jadutter/NGC602/Draft 1.JPG

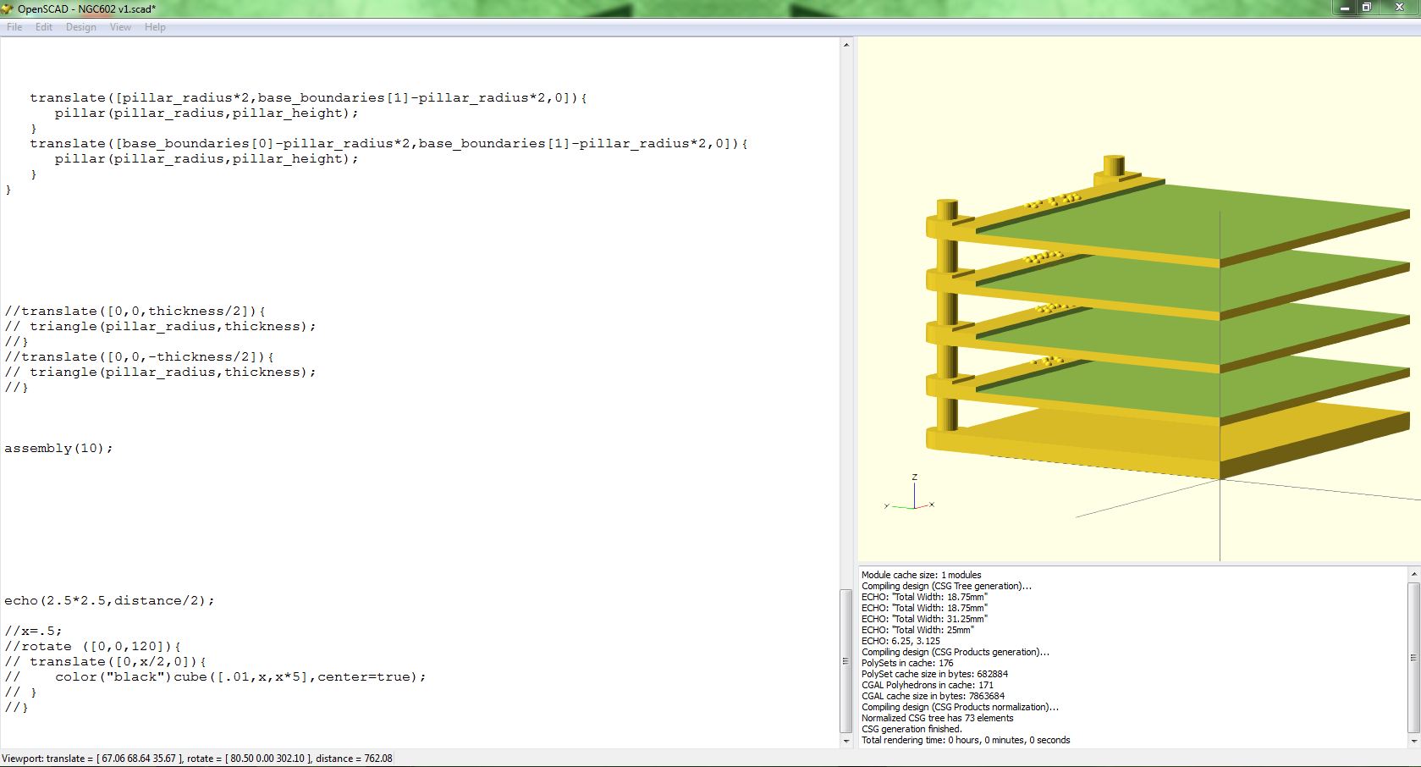
Draft 1.JPG
