jadutter/NGC602/Draft 2.JPG

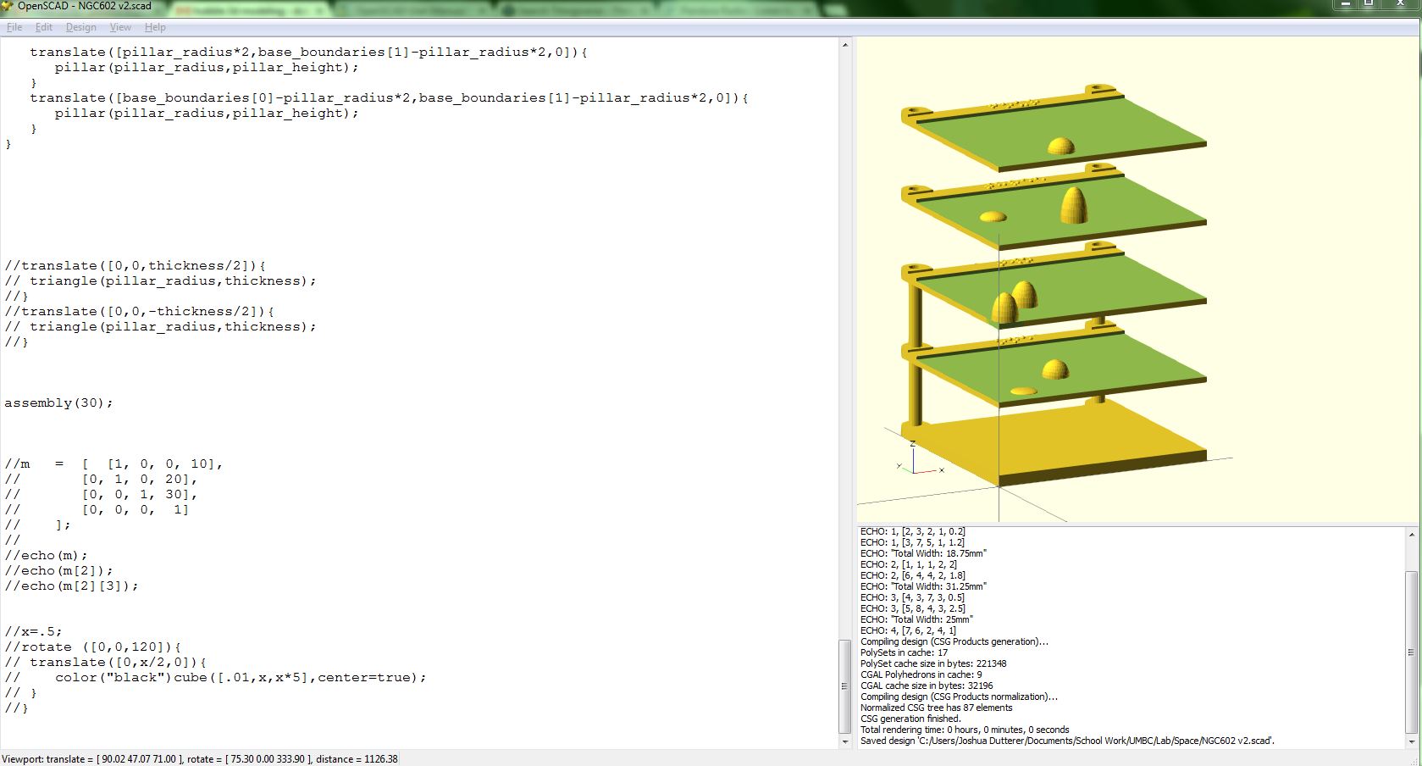
Draft 2.JPG
