jadutter/NGC602/Draft 3 All.JPG

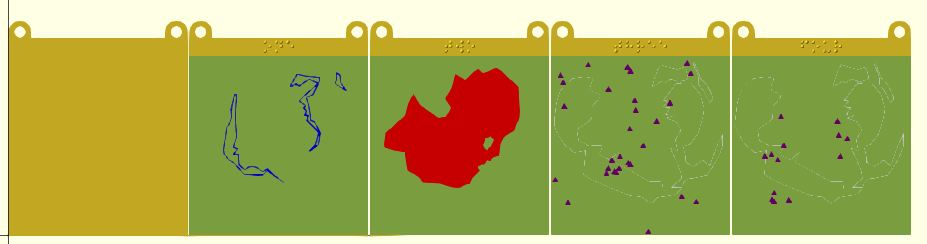
Draft 3 All.JPG
