jadutter/NGC602/Draft 3 plate 1.JPG

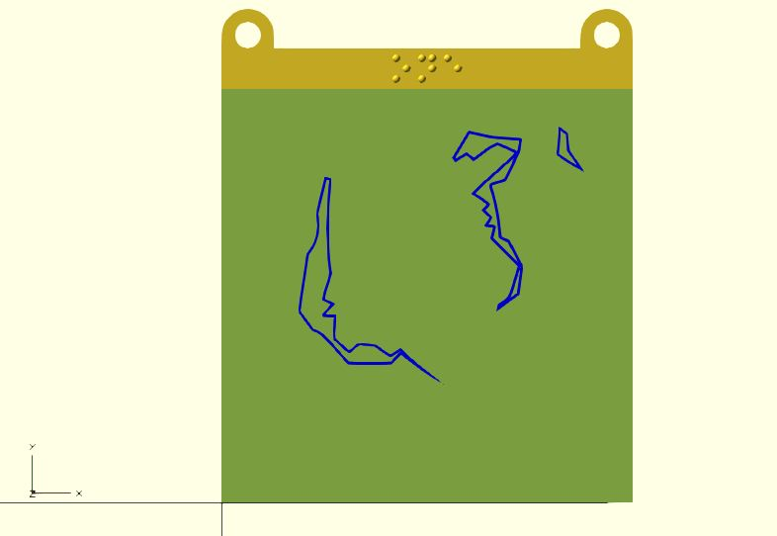
Draft 3 plate 1.JPG
