jadutter/NGC602/Draft 3 plate 2.JPG

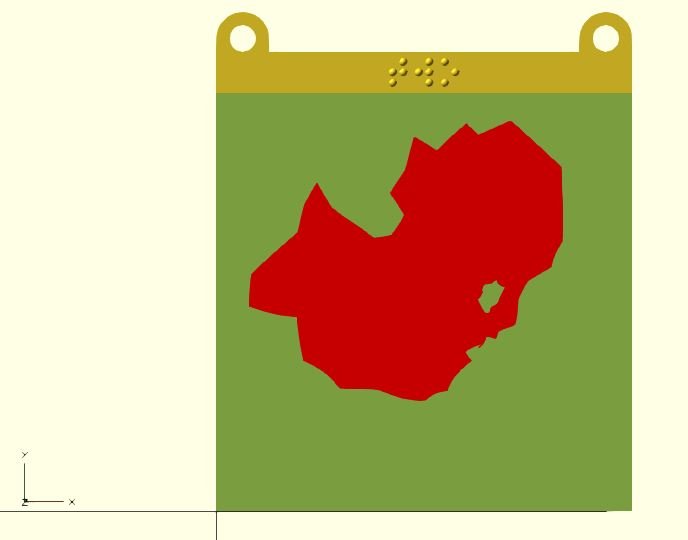
Draft 3 plate 2.JPG
