jadutter/NGC602/Draft 3 plate 3&4 again.JPG

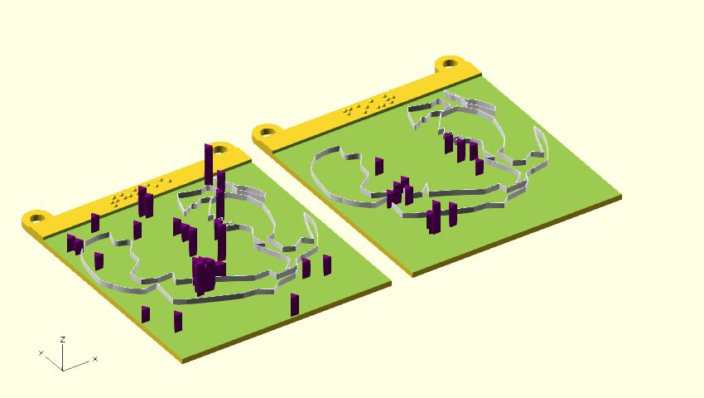
Draft 3 plate 3&4 again.JPG
