jadutter/NGC602/Draft 3 plate 4.JPG

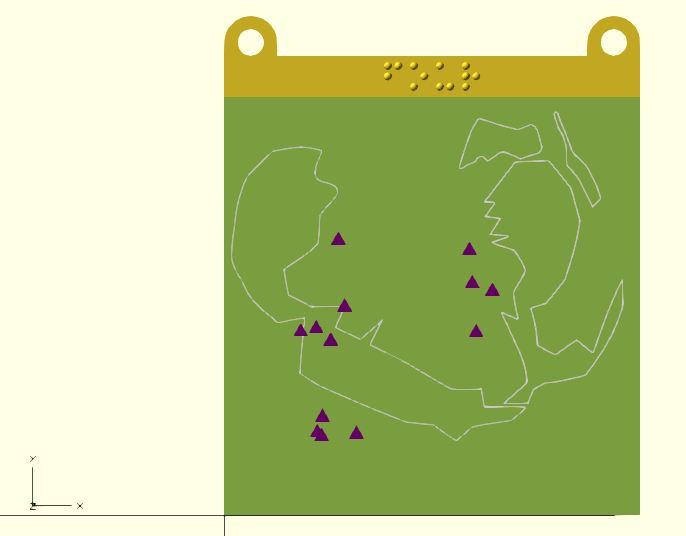
Draft 3 plate 4.JPG
