jadutter/NGC602/Draft 4 plate 3 again.JPG

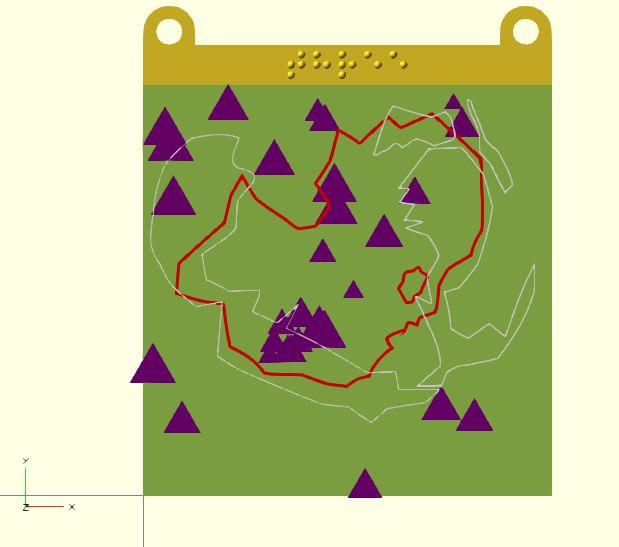
Draft 4 plate 3 again.JPG
