jadutter/NGC602/Draft 4 plate 3.JPG

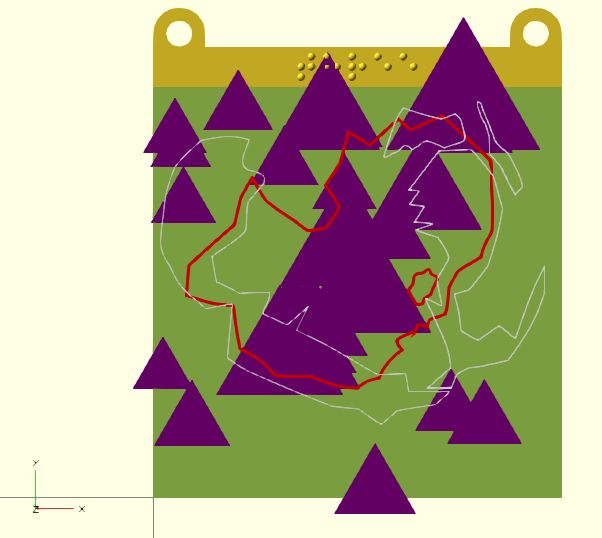
Draft 4 plate 3.JPG
