jadutter/NGC602/Draft 5 plate 3&4.JPG

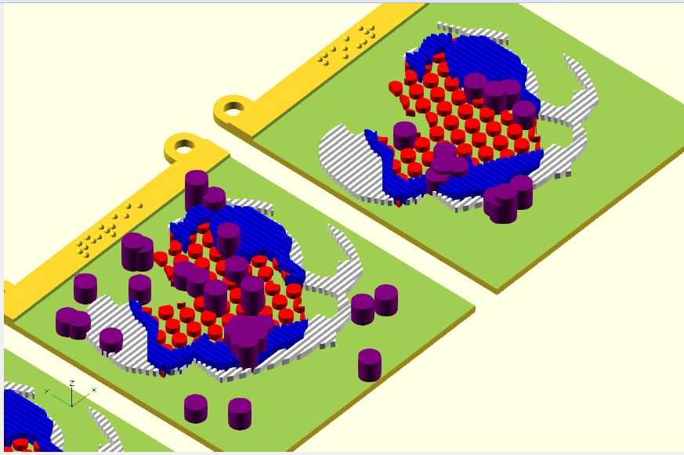
Draft 5 plate 3&4.JPG
