jadutter/NGC602/Extruded Gas.JPG

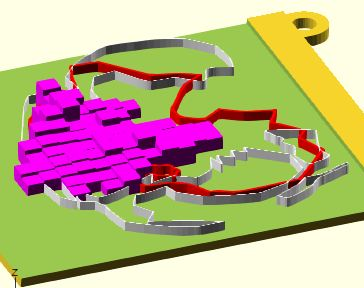
Extruded Gas.JPG
