jadutter/NGC602/Grice-RevisedNGC602Textures.jpg

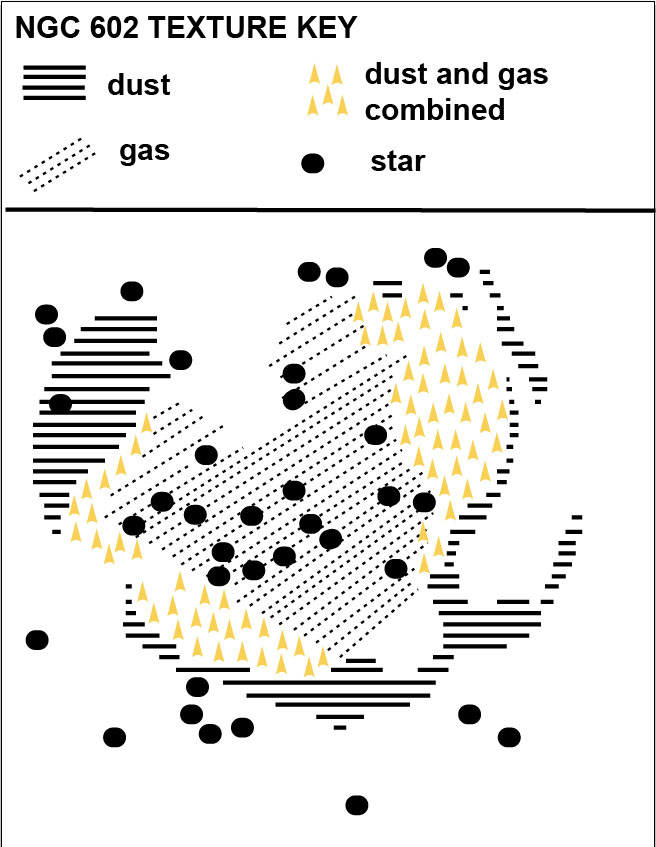
Grice-RevisedNGC602Textures.jpg
