jadutter/NGC602/IMG_20130621_184517_456.jpg

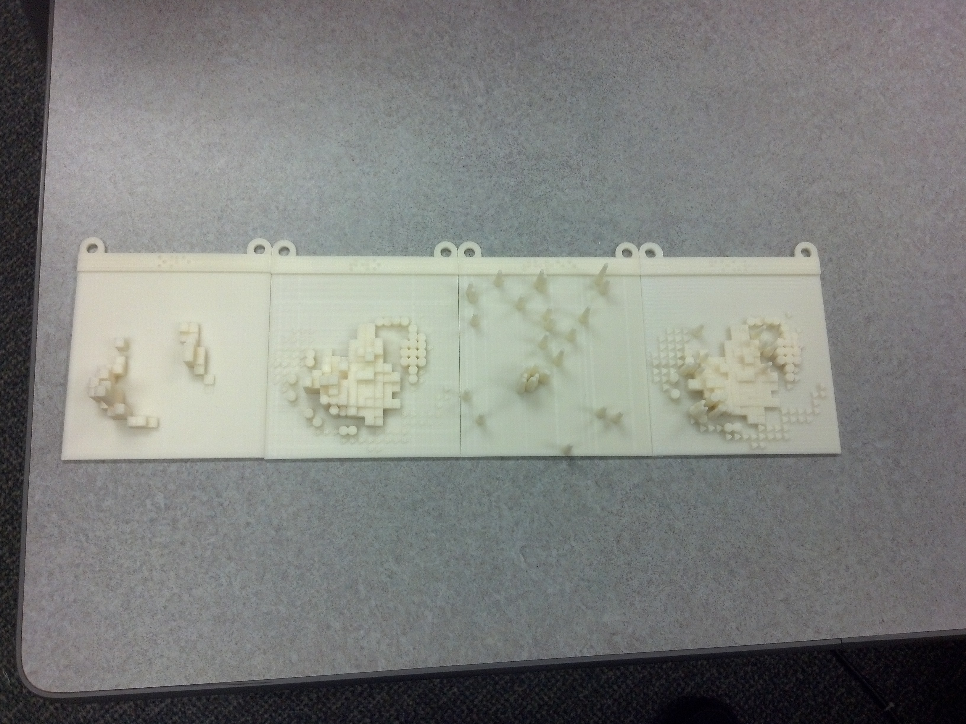
IMG_20130621_184517_456.jpg
