jadutter/NGC602/IMG_20130621_184525_783.jpg

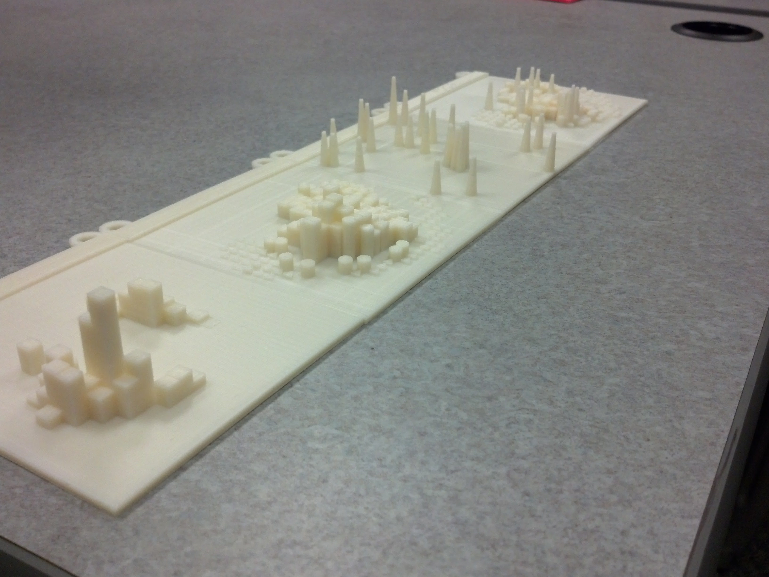
IMG_20130621_184525_783.jpg
