jadutter/NGC602/IMG_20130625_030818_657.jpg

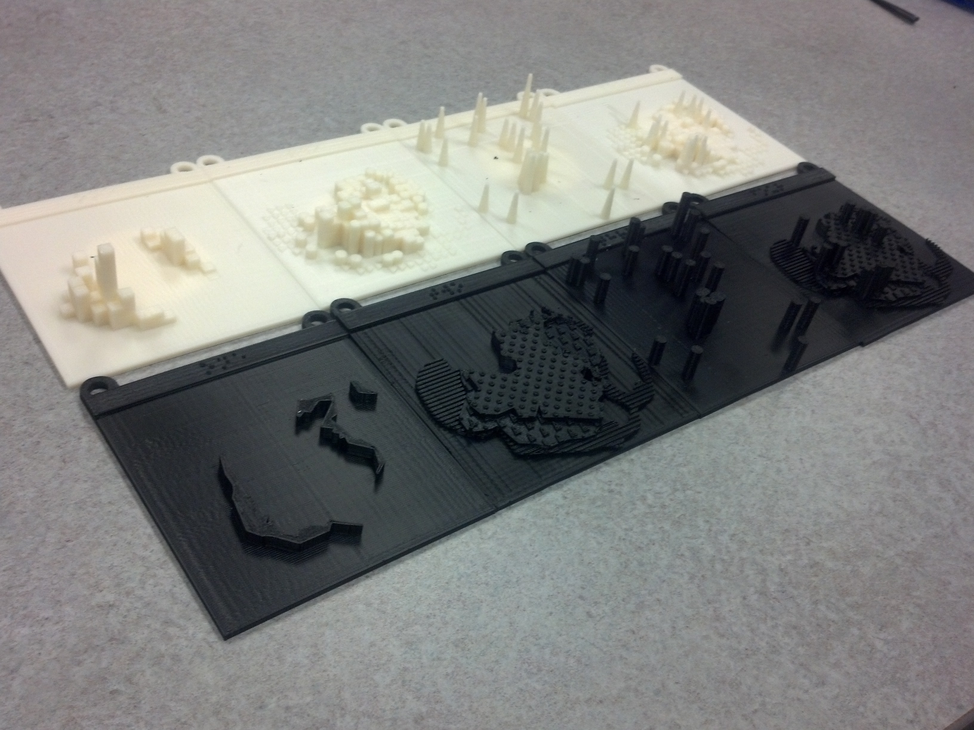
IMG_20130625_030818_657.jpg
