jadutter/NGC602/IMG_20130625_030837_733.jpg

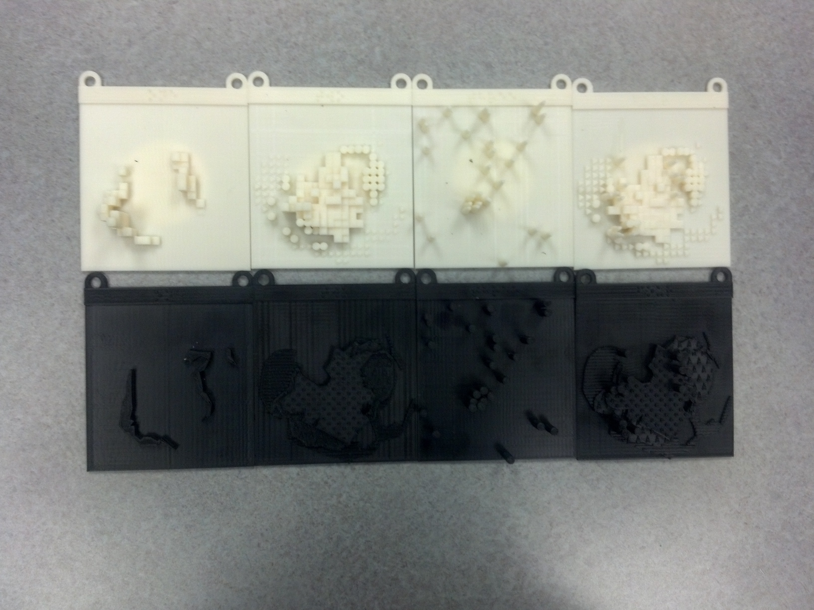
IMG_20130625_030837_733.jpg
