jadutter/NGC602/IMG_20130625_030843_815.jpg

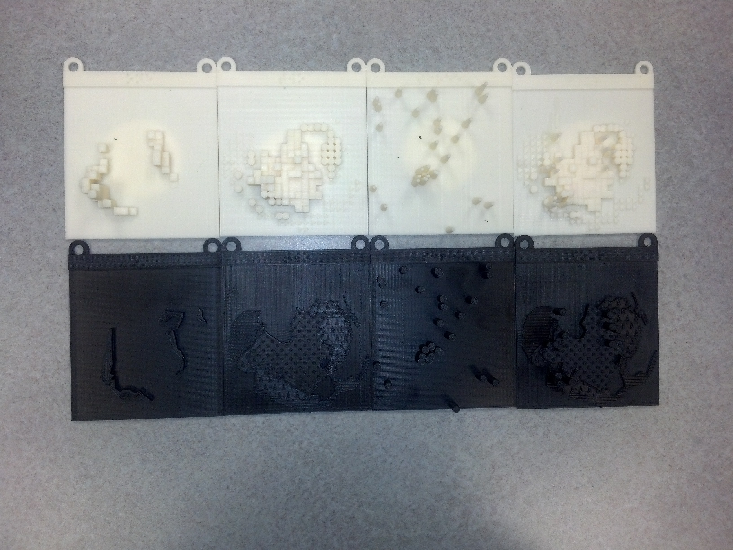
IMG_20130625_030843_815.jpg
