jadutter/NGC602/IMG_20130625_030916_029.jpg

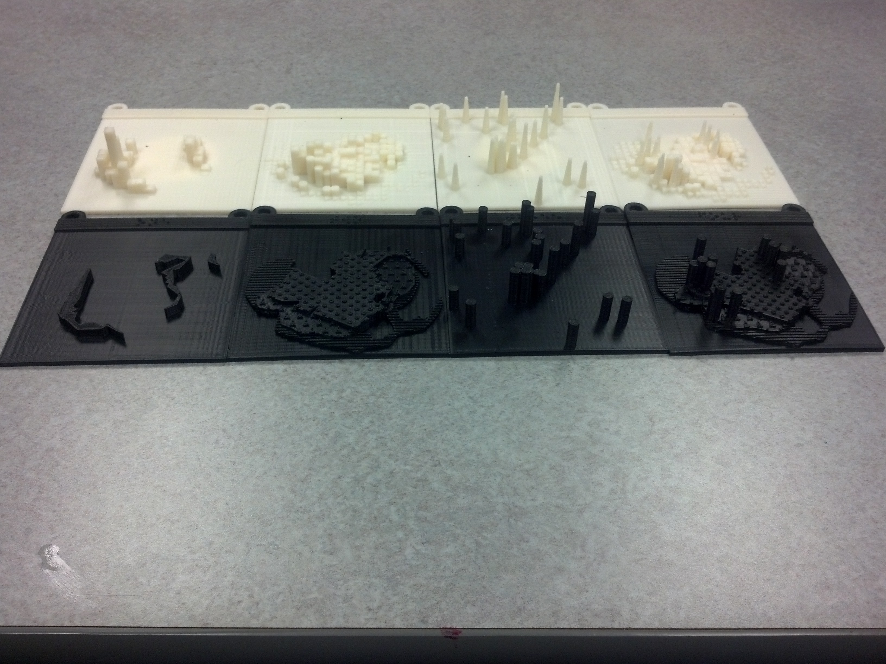
IMG_20130625_030916_029.jpg
