jadutter/NGC602/IMG_20130625_030923_143.jpg

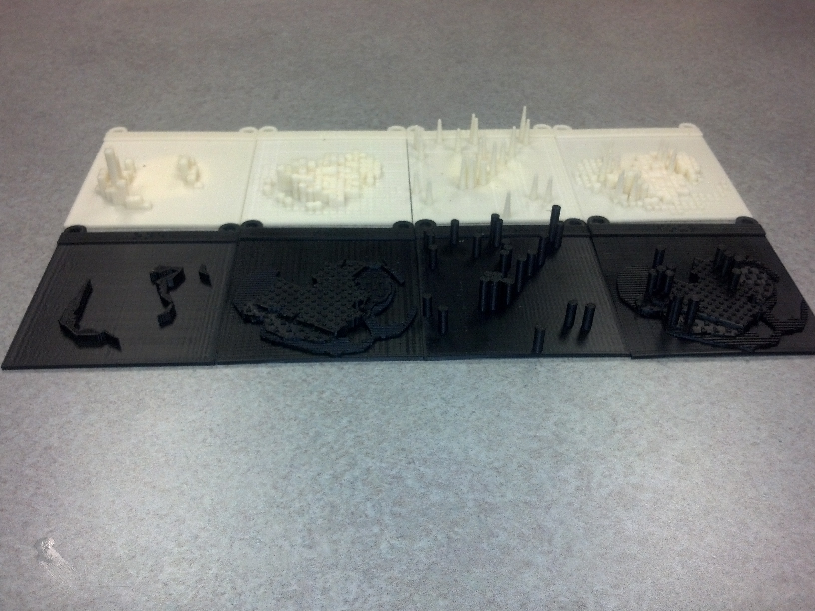
IMG_20130625_030923_143.jpg
