jadutter/NGC602/IMG_20130625_030944_318.jpg

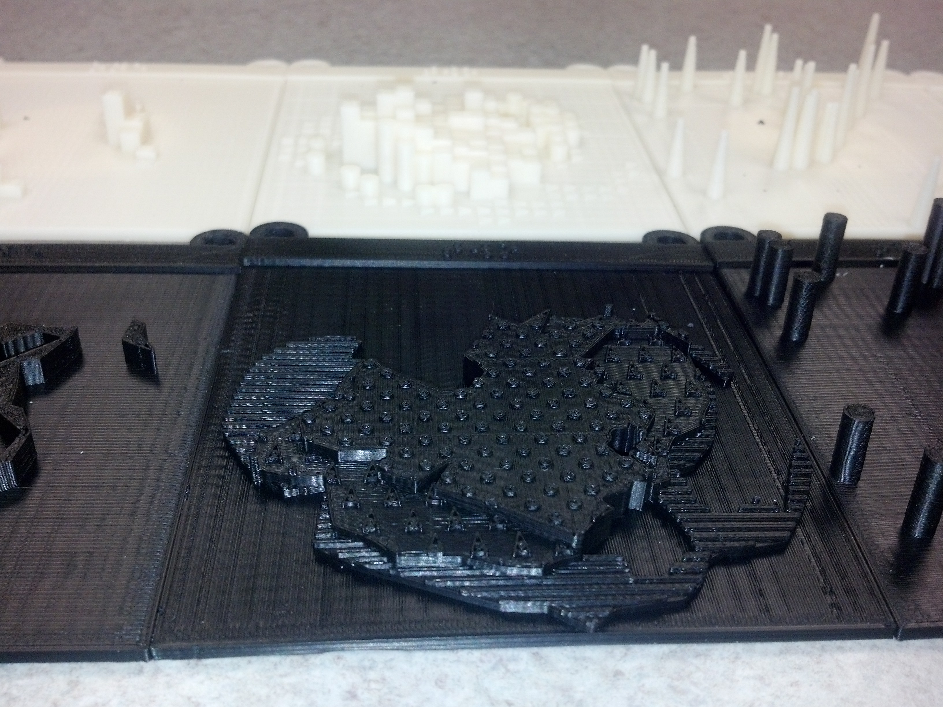
IMG_20130625_030944_318.jpg
