jadutter/NGC602/IMG_20130625_030954_769.jpg

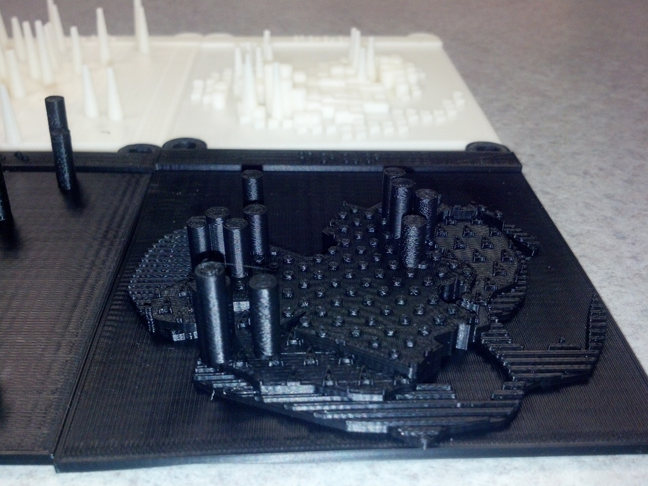
IMG_20130625_030954_769.jpg
