jadutter/NGC602/NGC602 v7 Left Plate 2&3&4.JPG

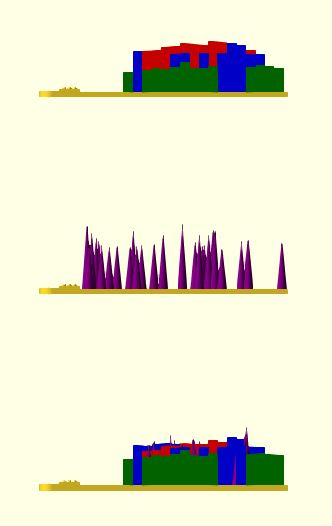
NGC602 v7 Left Plate 2&3&4.JPG
