jadutter/NGC602/NGC602 v7 Left Plate 3, again.JPG

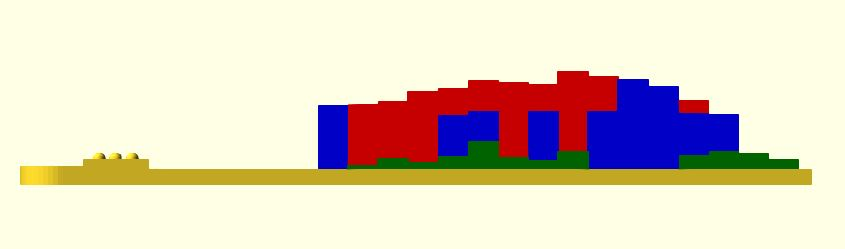
NGC602 v7 Left Plate 3, again.JPG
