jadutter/NGC602/NGC602 v7 Left Plate 4, again.JPG

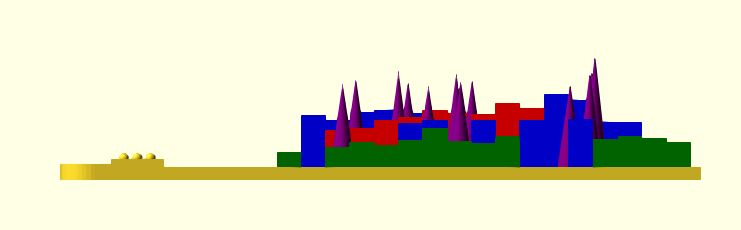
NGC602 v7 Left Plate 4, again.JPG
