jadutter/NGC602/NGC602 v7 Plate 3 Scaled.JPG

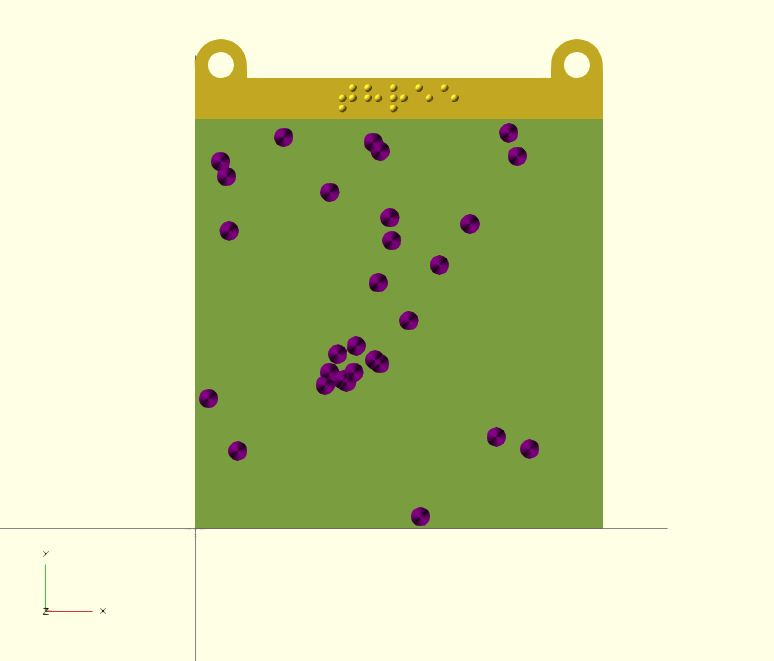
NGC602 v7 Plate 3 Scaled.JPG
