jadutter/NGC602/NGC602 v7 Plate 3 Scaling example.JPG

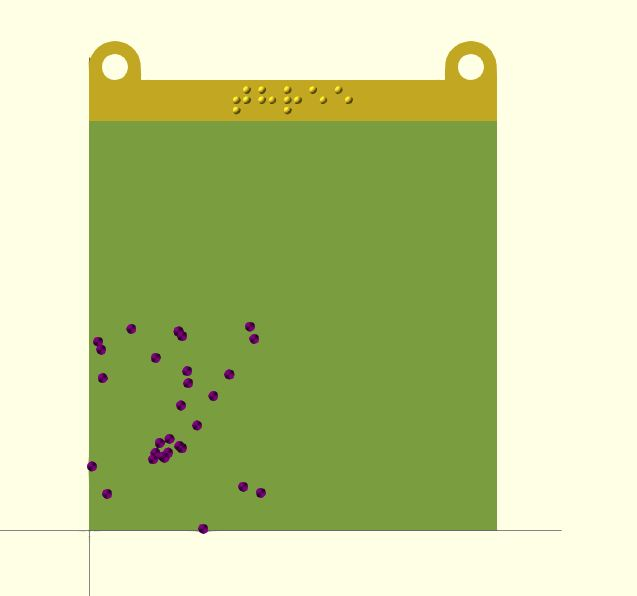
NGC602 v7 Plate 3 Scaling example.JPG
