jadutter/NGC602/NGC602 v7 Plate 3 Unscaled.JPG

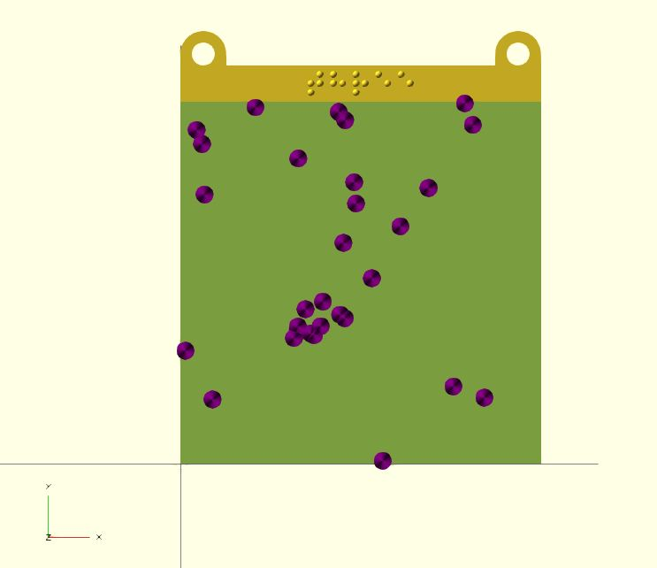
NGC602 v7 Plate 3 Unscaled.JPG
