jadutter/NGC602/Plates 3&4.JPG

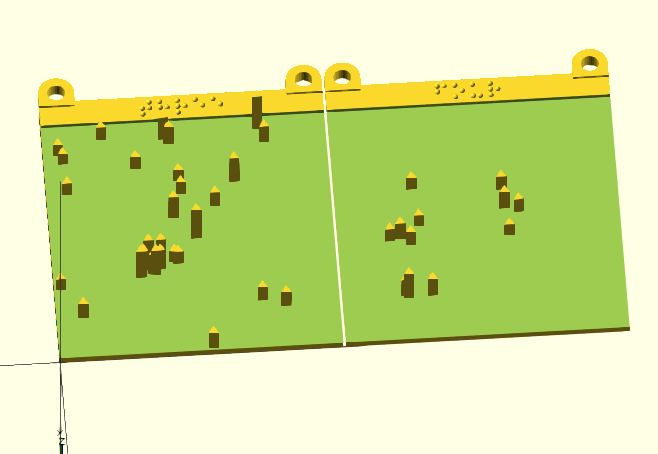
Plates 3&4.JPG
