jadutter/NGC602/Proof 1.JPG

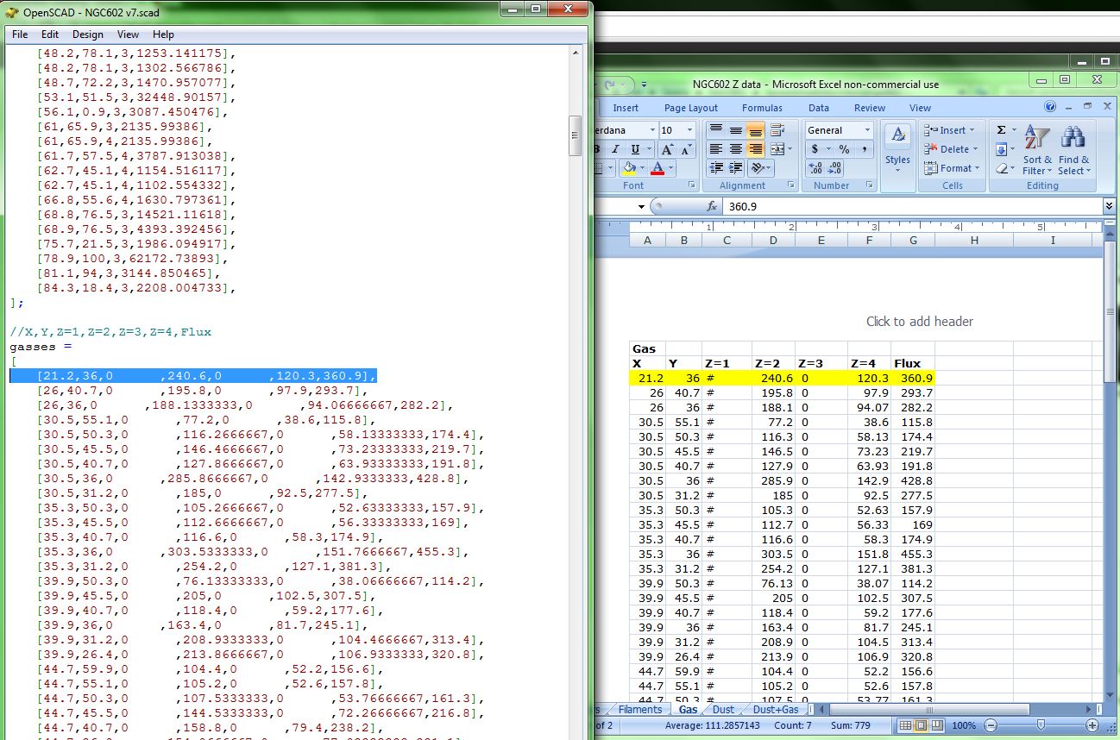
Proof 1.JPG
