jadutter/NGC602/Proof 2.JPG

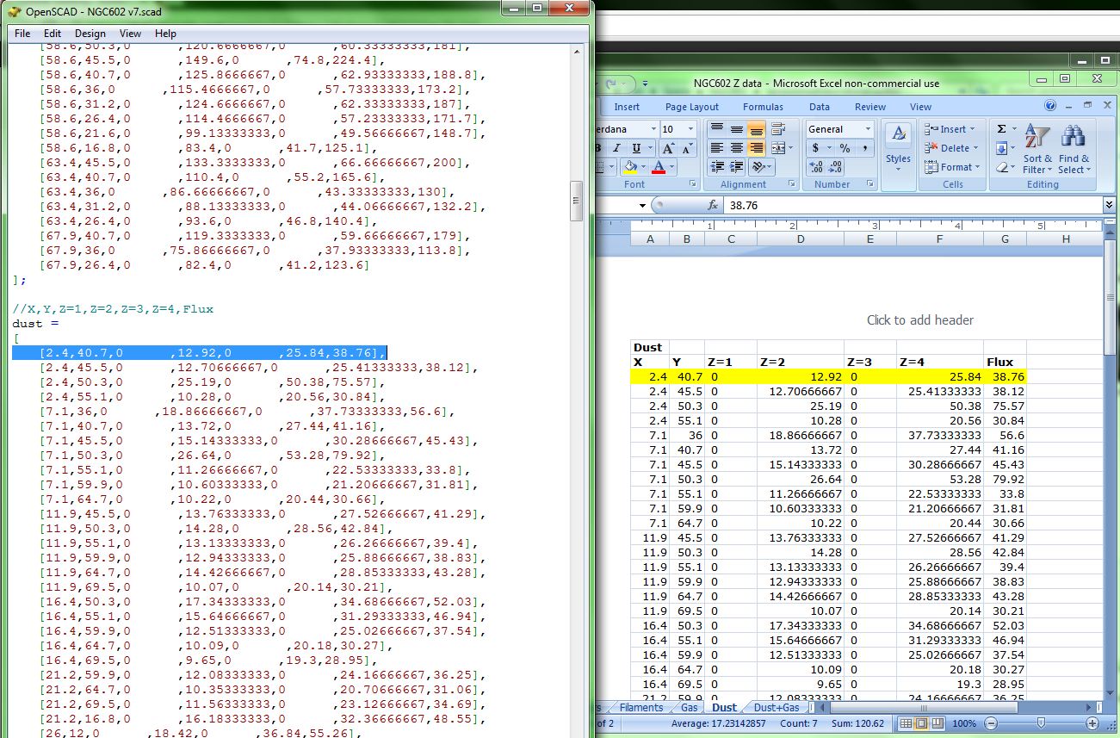
Proof 2.JPG
