jadutter/NGC602/Proof 3.JPG

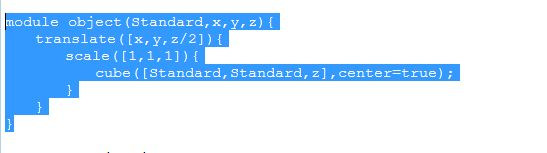
Proof 3.JPG
