jadutter/NGC602/Proof 4.JPG

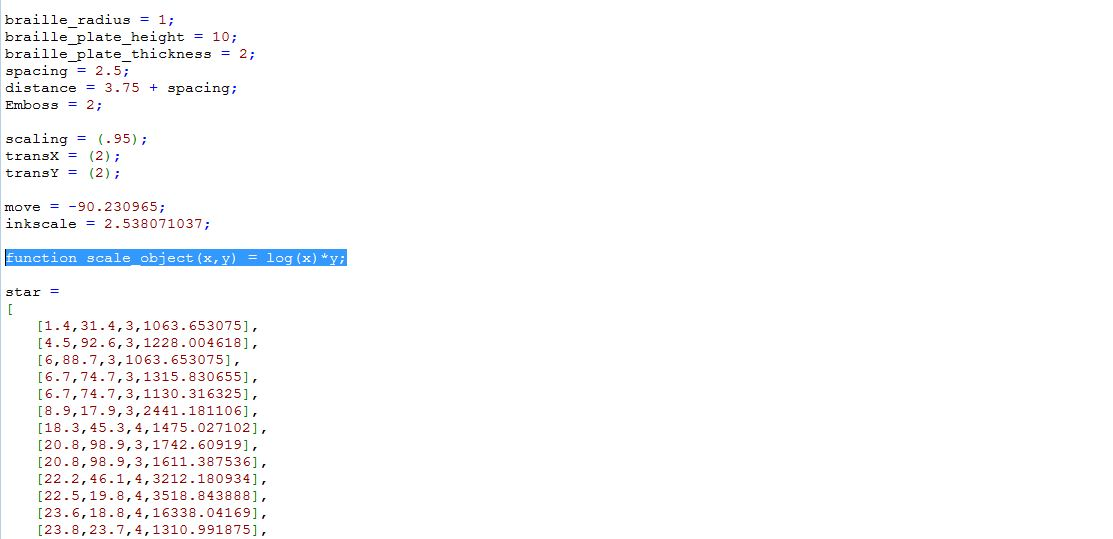
Proof 4.JPG
