jadutter/NGC602/Proof 5.JPG

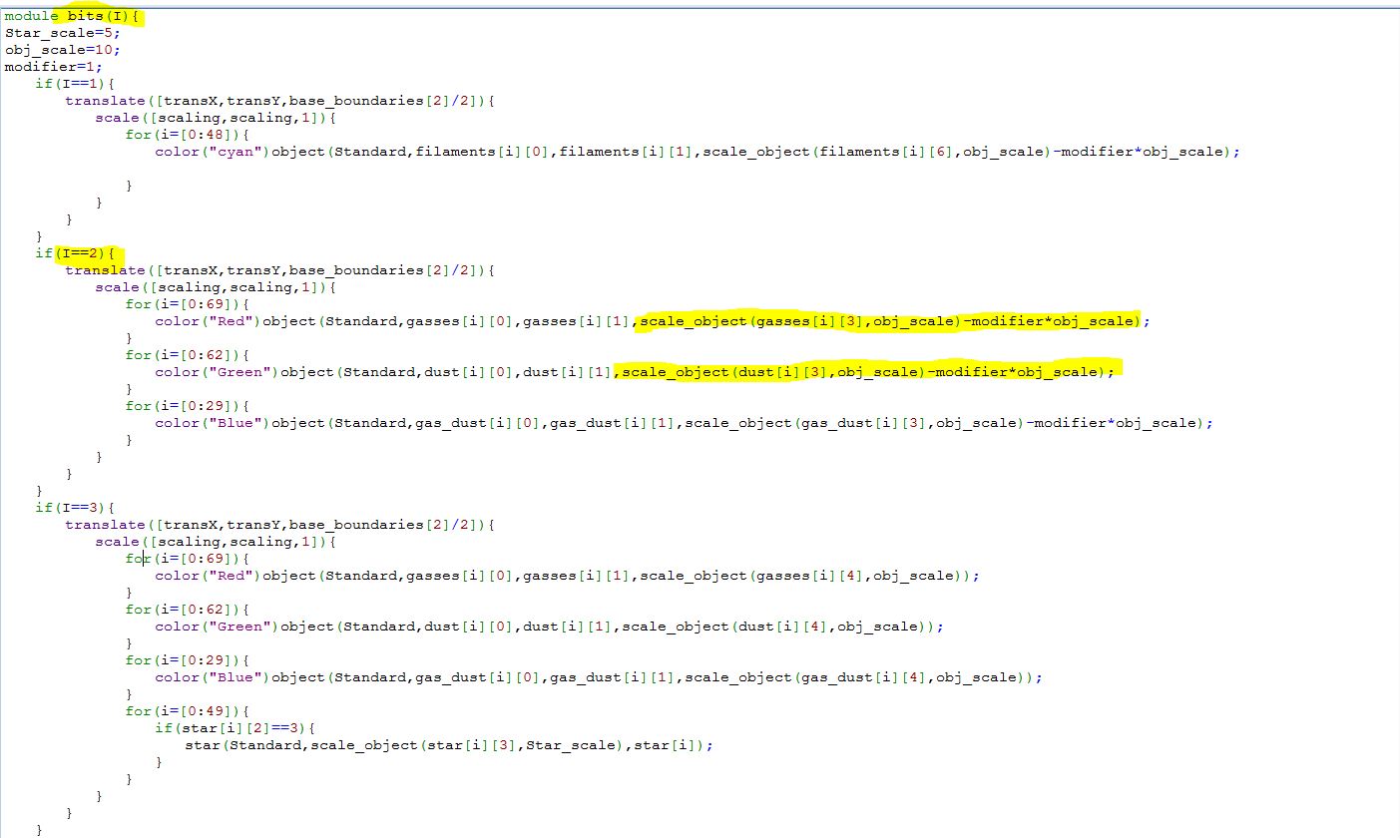
Proof 5.JPG
