jadutter/NGC602/Proof 6.JPG

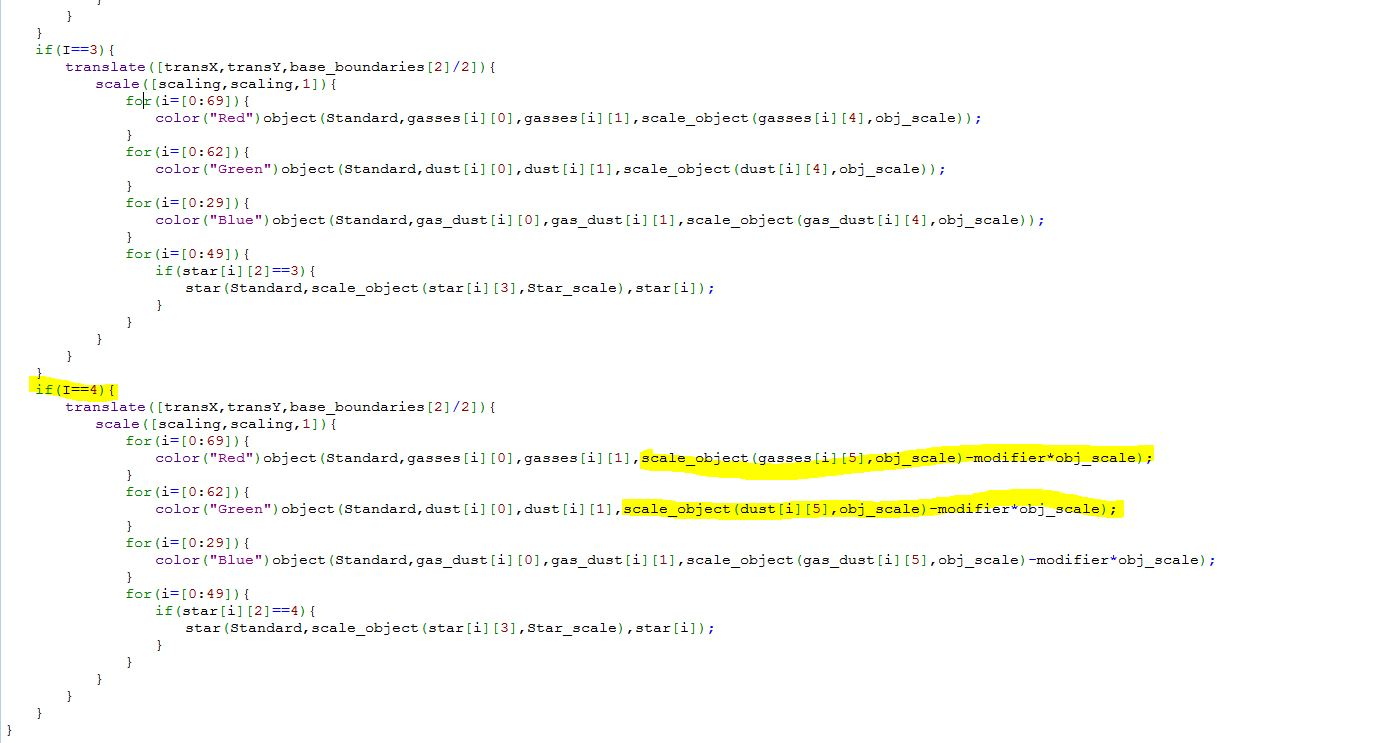
Proof 6.JPG
