jadutter/NGC602/Proof 7.JPG

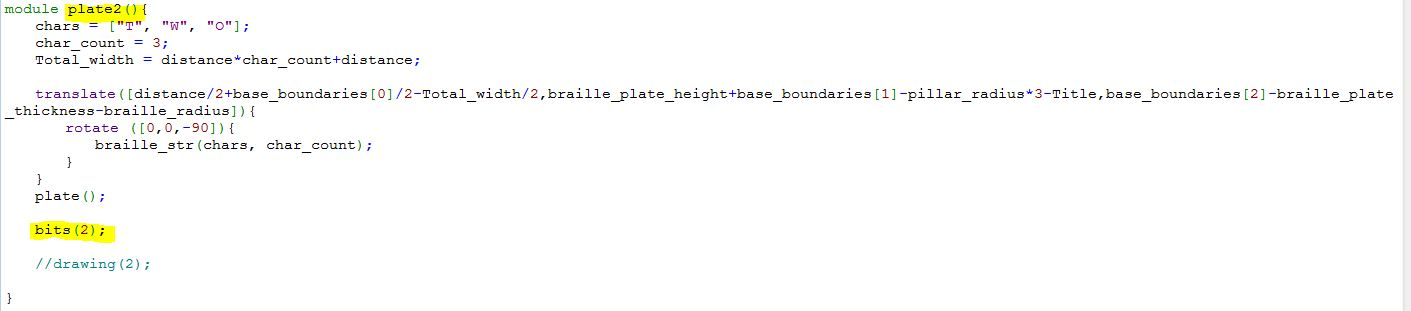
Proof 7.JPG
