jadutter/NGC602/Proof 8.JPG

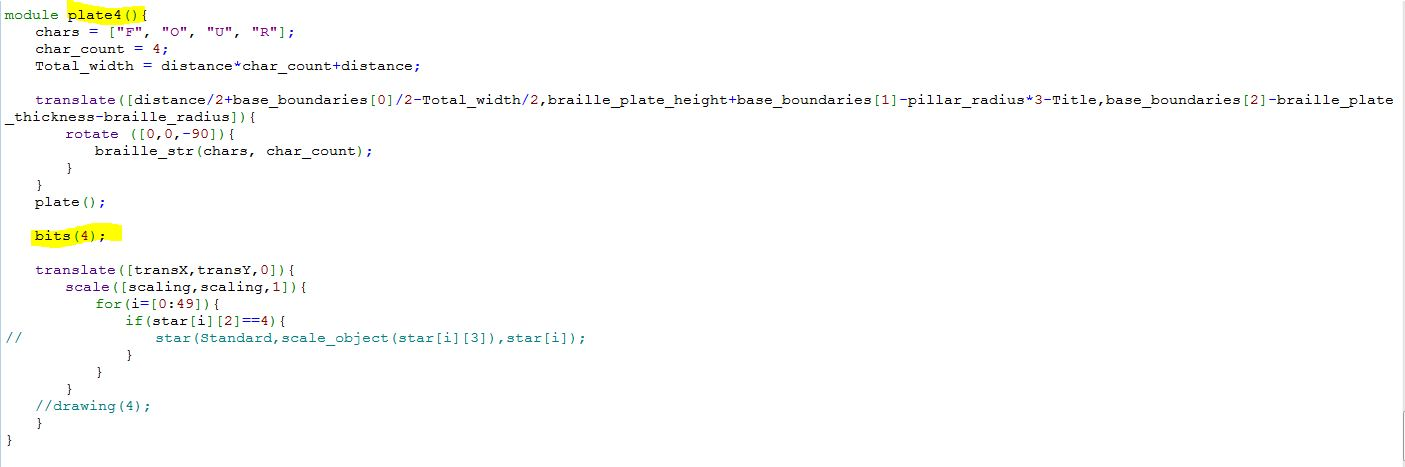
Proof 8.JPG
