jadutter/NGC602/Proof 9.JPG

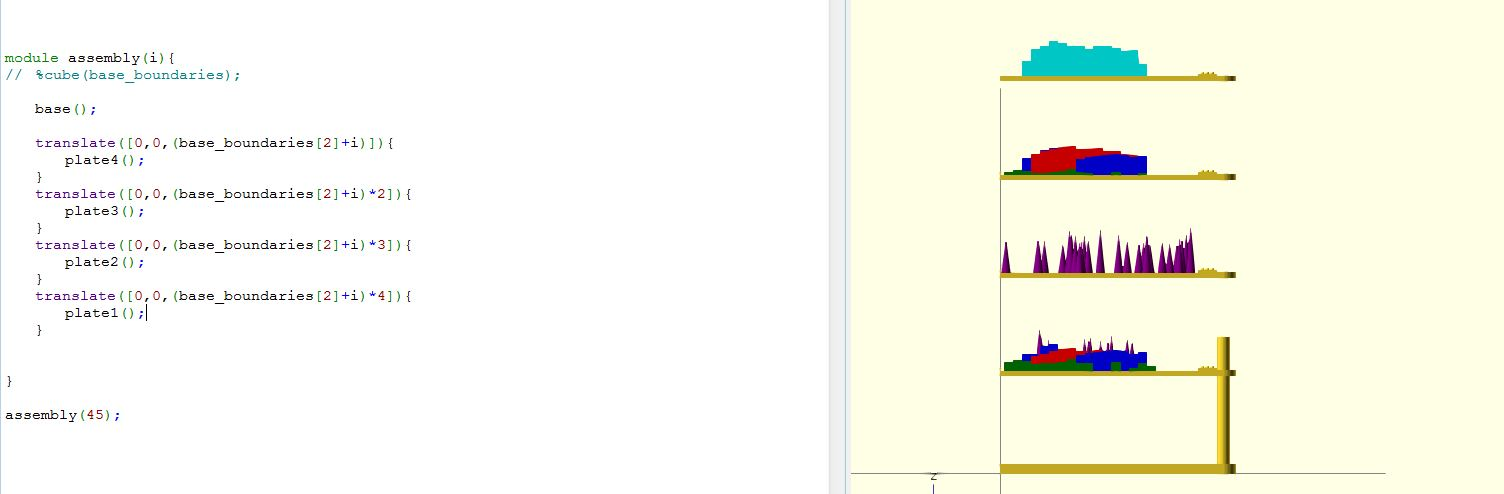
Proof 9.JPG
