jadutter/NGC602/Proof 10.JPG

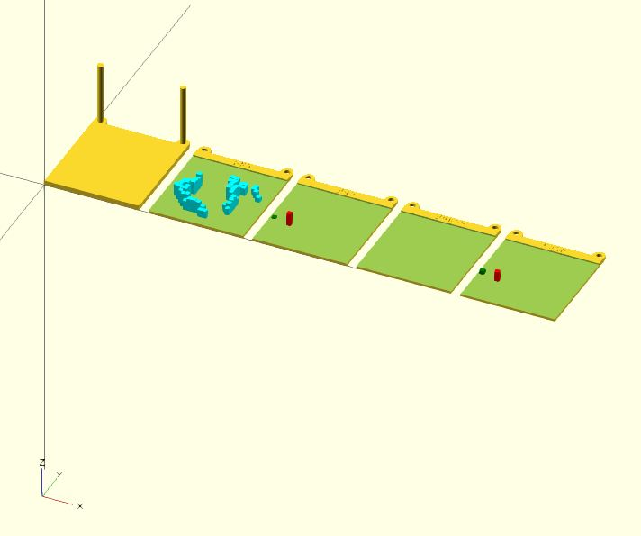
Proof 10.JPG
