jadutter/NGC602/Proof 11.JPG

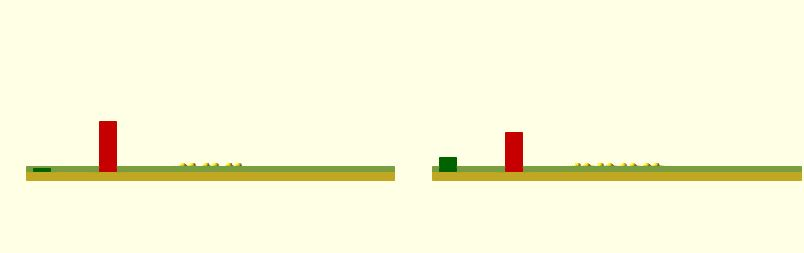
Proof 11.JPG
