jadutter/NGC602/spreadsheetdescribingngc602/Central Cluster.png

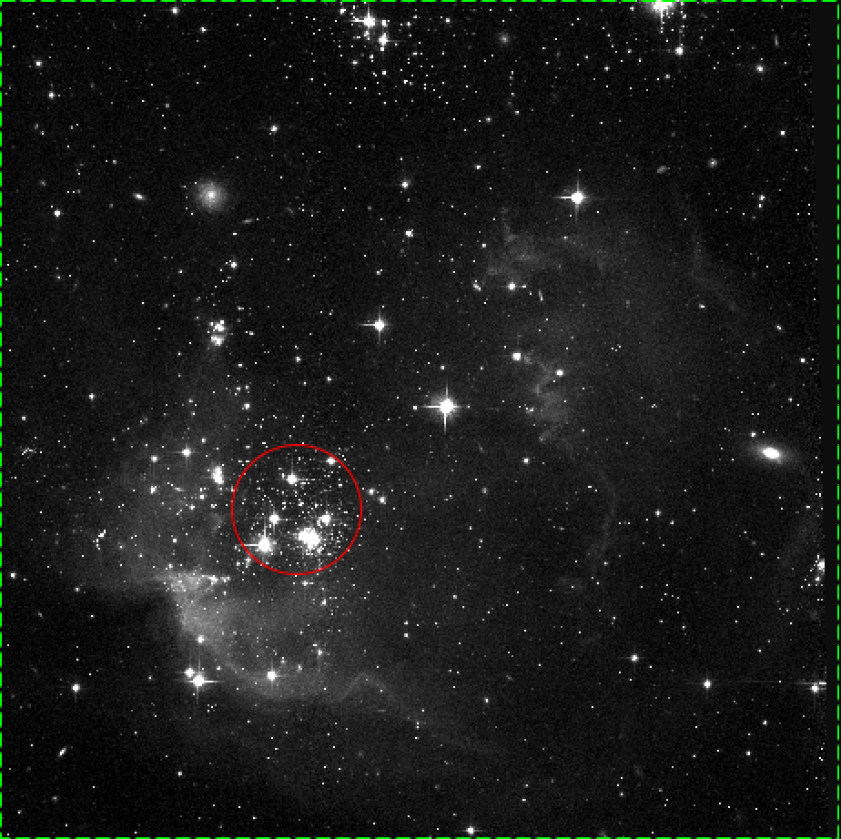
spreadsheetdescribingngc602/Central Cluster.png
