jadutter/NGC602/spreadsheetdescribingngc602/Dust.png

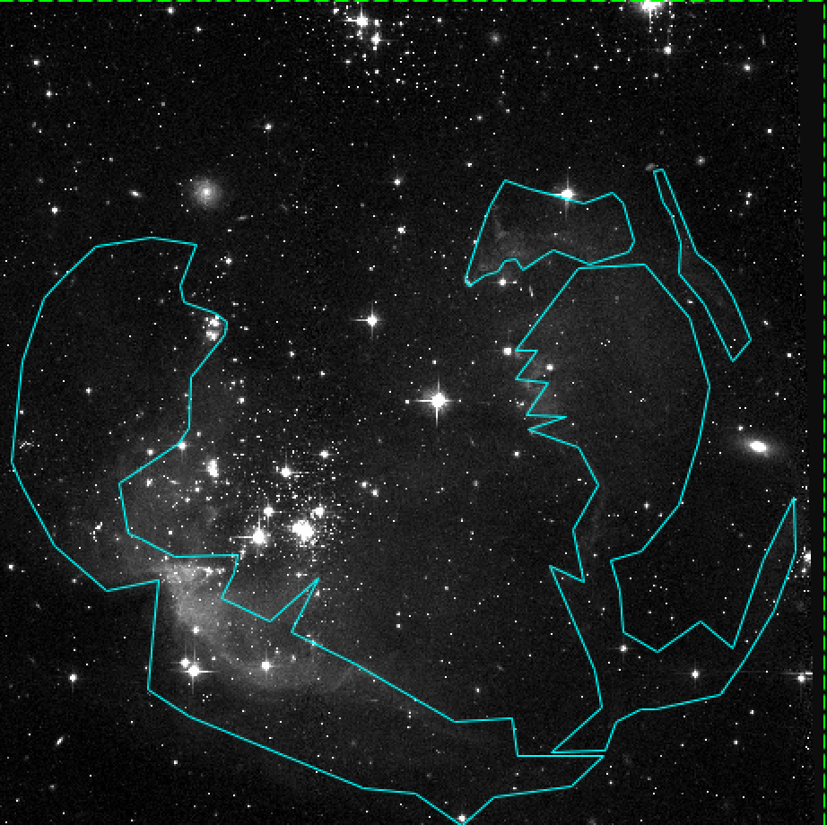
spreadsheetdescribingngc602/Dust.png
