jadutter/NGC602/spreadsheetdescribingngc602/Gas.png

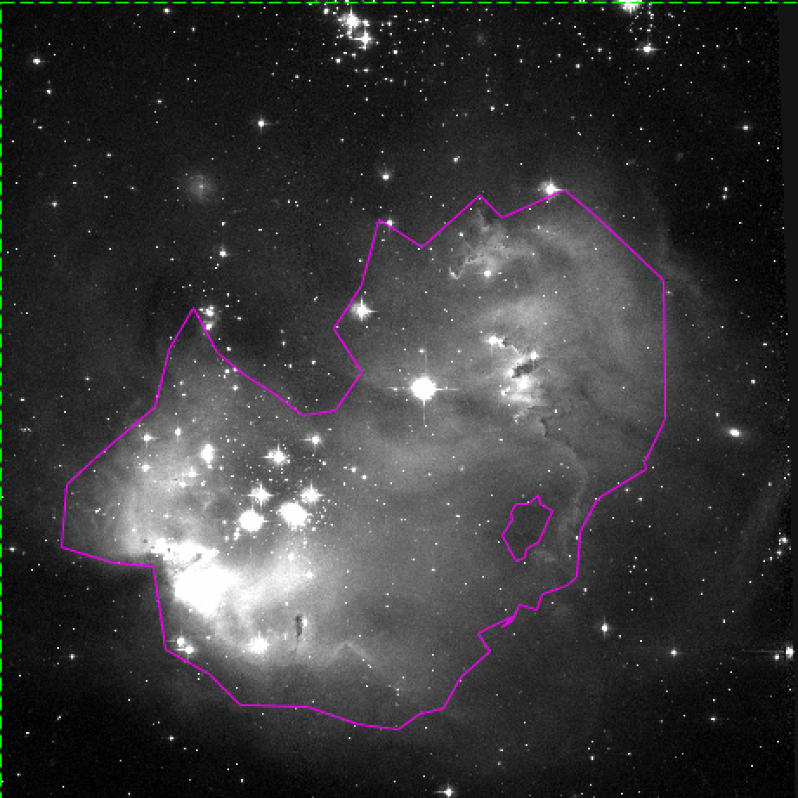
spreadsheetdescribingngc602/Gas.png
