jadutter/NGC602/spreadsheetdescribingngc602/NGC 602 Frame.png

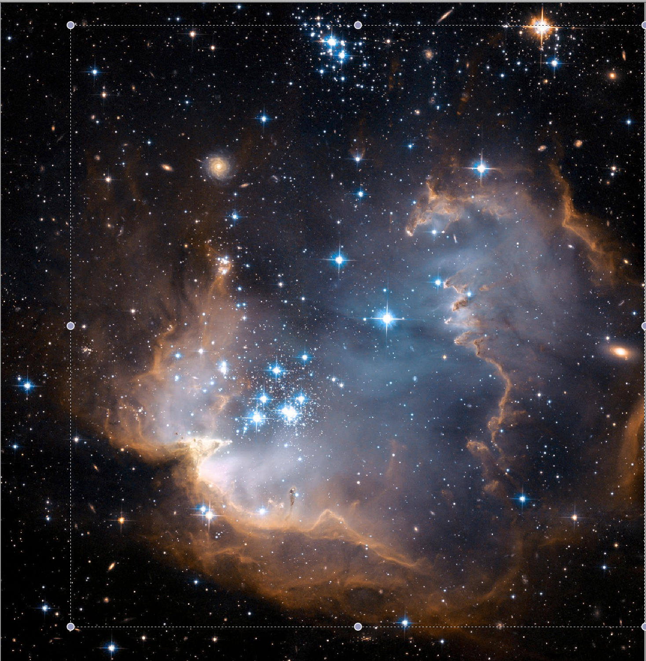
spreadsheetdescribingngc602/NGC 602 Frame.png
