jadutter/NGC602/spreadsheetdescribingngc602/Overlay.png

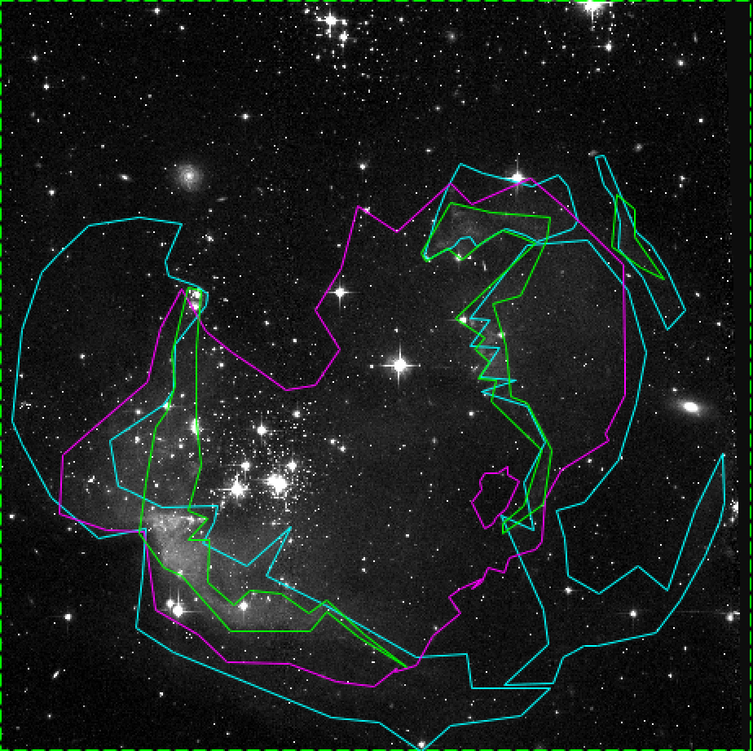
spreadsheetdescribingngc602/Overlay.png
