jadutter/NGC602/Texture.jpg

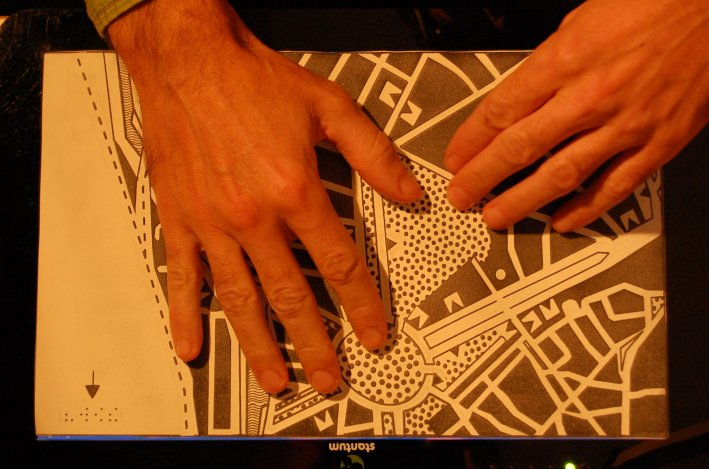
Texture.jpg
