jadutter/NGC602/Textures NGC602 v4.JPG

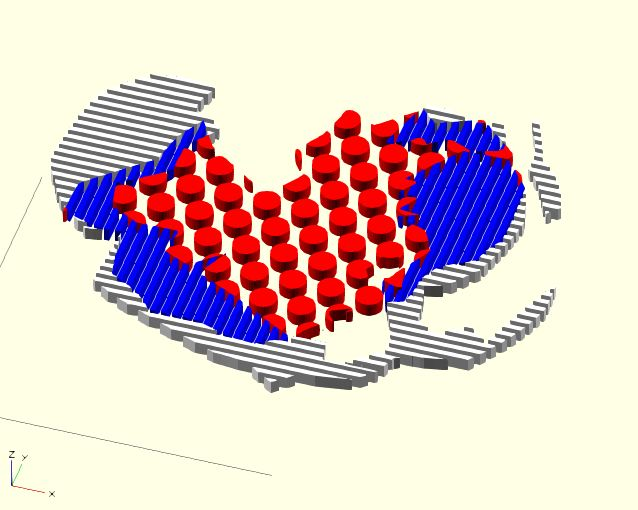
Textures NGC602 v4.JPG
