jadutter/NGC602/v7/plate 2 NGC602 v7.stl

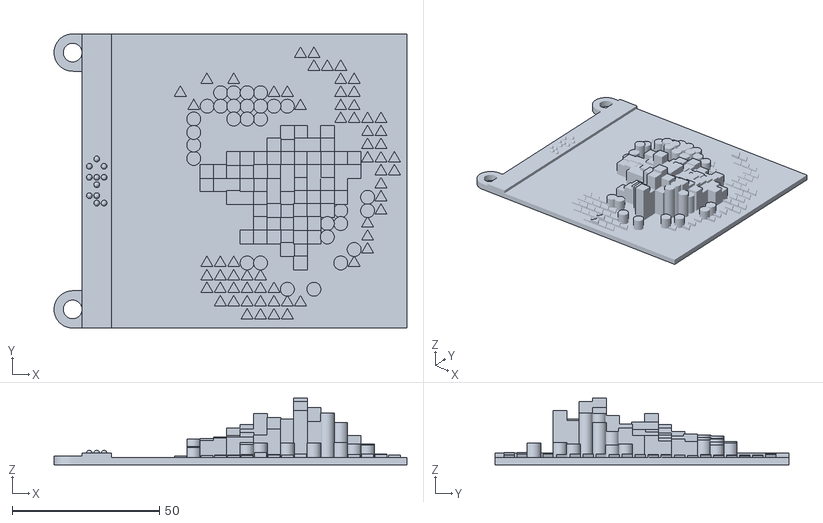
[picture p69: CAD file, 2013-06-21]
v7/plate 2 NGC602 v7.stl
120.0 x 100.0 x 22.7
