jadutter/NGC602/plate 3 NGC602 v6.stl

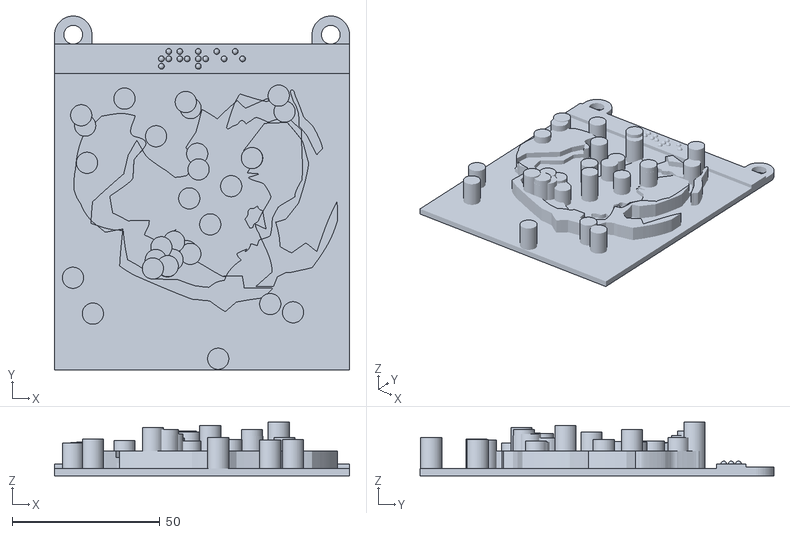
[picture p70: CAD file, 2013-06-17]
plate 3 NGC602 v6.stl
100.0 x 120.0 x 18.2
