jadutter/NGC602/NGC_602.dxf

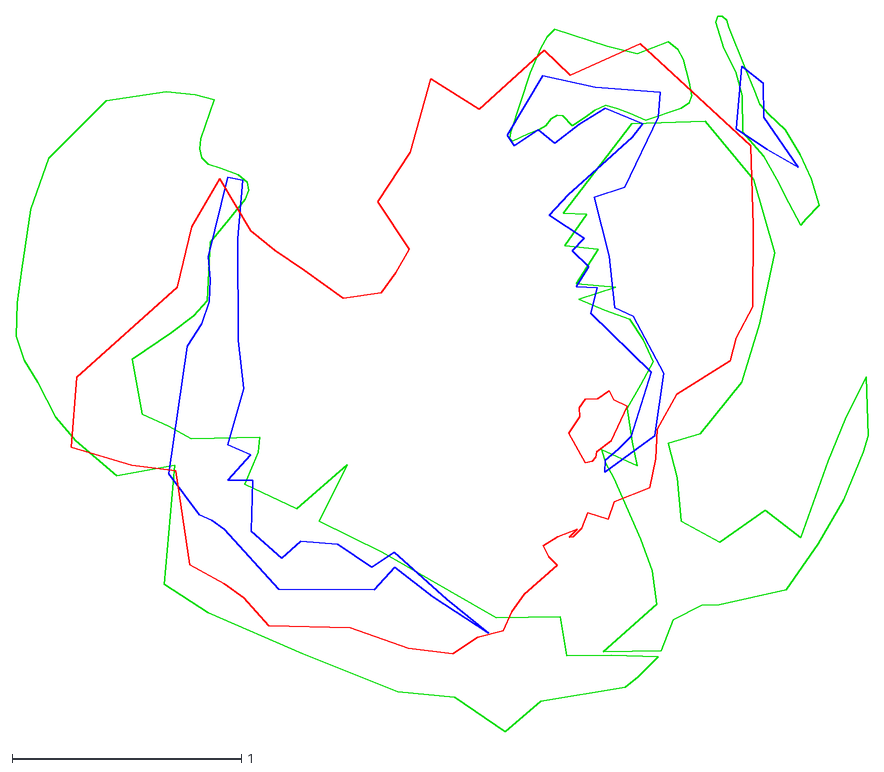
[picture p71: CAD file, 2013-06-17]
NGC_602.dxf
3.72 x 3.12
