jadutter/NGC602/Base NGC602 v3.stl

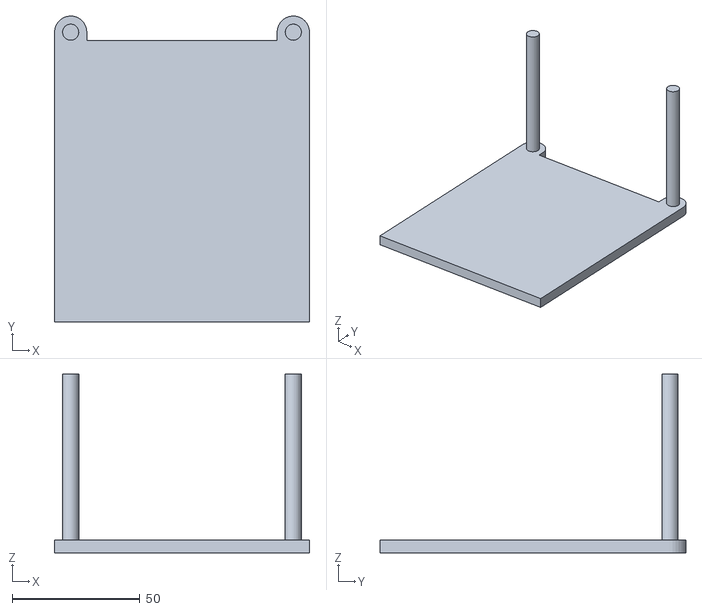
[picture p72: CAD file, 2013-06-17]
Base NGC602 v3.stl
100.0 x 120.0 x 70.0
