jadutter/NGC602/Test.dxf

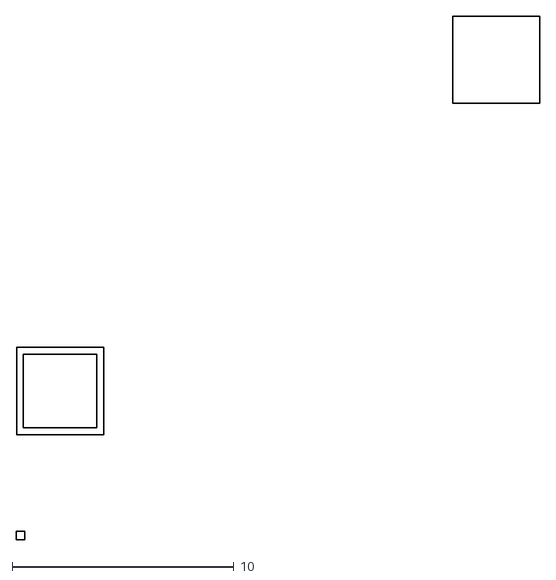
[picture p73: CAD file, 2013-06-17]
Test.dxf
23.6 x 23.6
