jadutter/NGC602/NGC602 v7 Assembly, Left.JPG

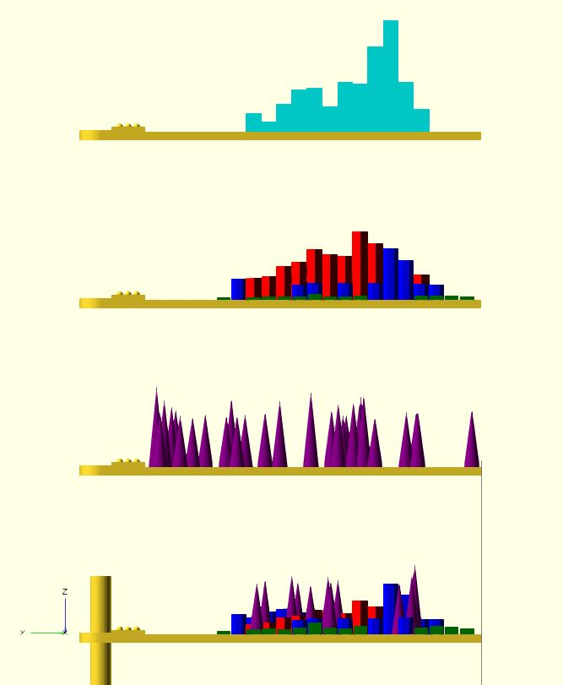
NGC602 v7 Assembly, Left.JPG
