jadutter/NGC602/NGC602 v7 Iso Assembly, B.JPG

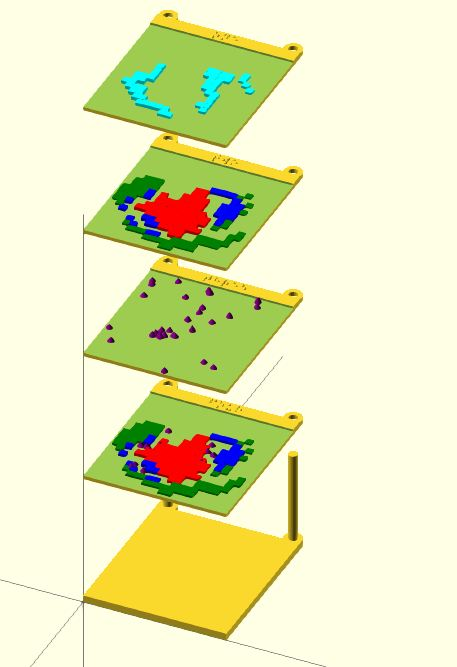
NGC602 v7 Iso Assembly, B.JPG
