jadutter/NGC602/NGC602 v7 Iso Assembly, C.JPG

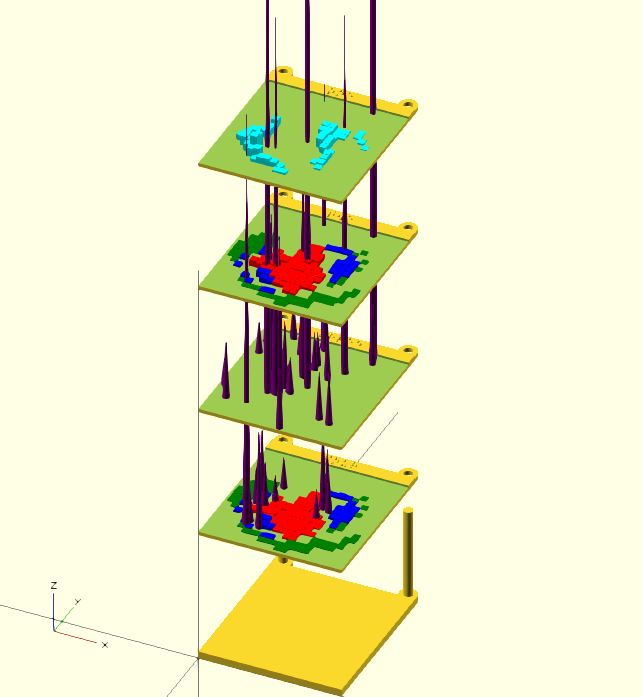
NGC602 v7 Iso Assembly, C.JPG
