jadutter/NGC602/NGC602 v7 Iso Assembly, D again.JPG

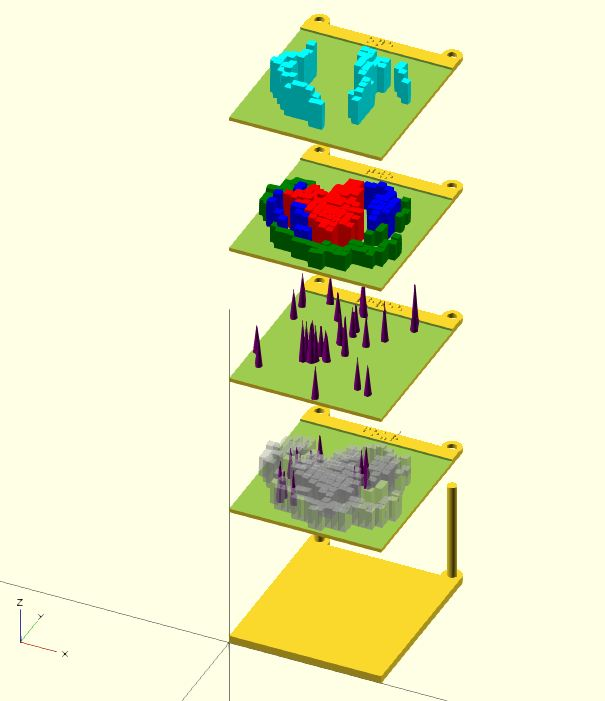
NGC602 v7 Iso Assembly, D again.JPG
