jadutter/NGC602/NGC602 v7 Iso Assembly, E.JPG

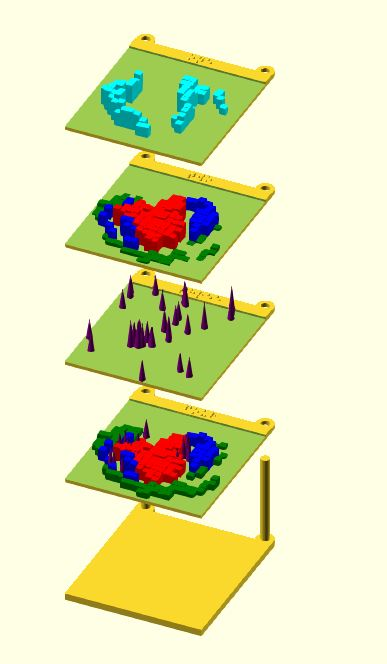
NGC602 v7 Iso Assembly, E.JPG
