jadutter/NGC602/Star Test Data CSV.JPG

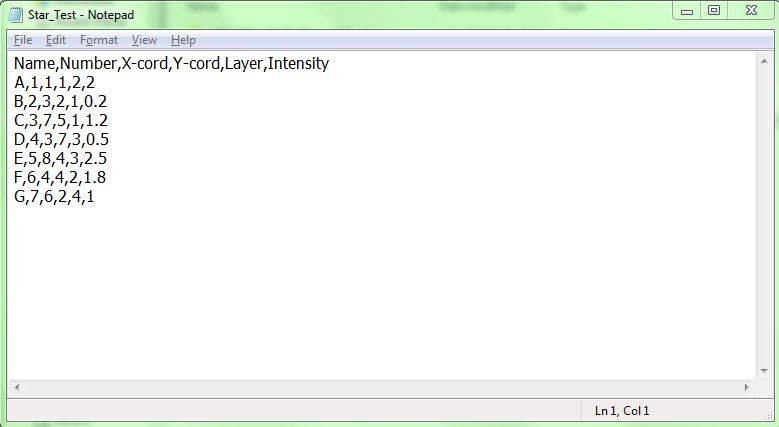
Star Test Data CSV.JPG
