jadutter/NGC602/Star Test Data Excel.JPG

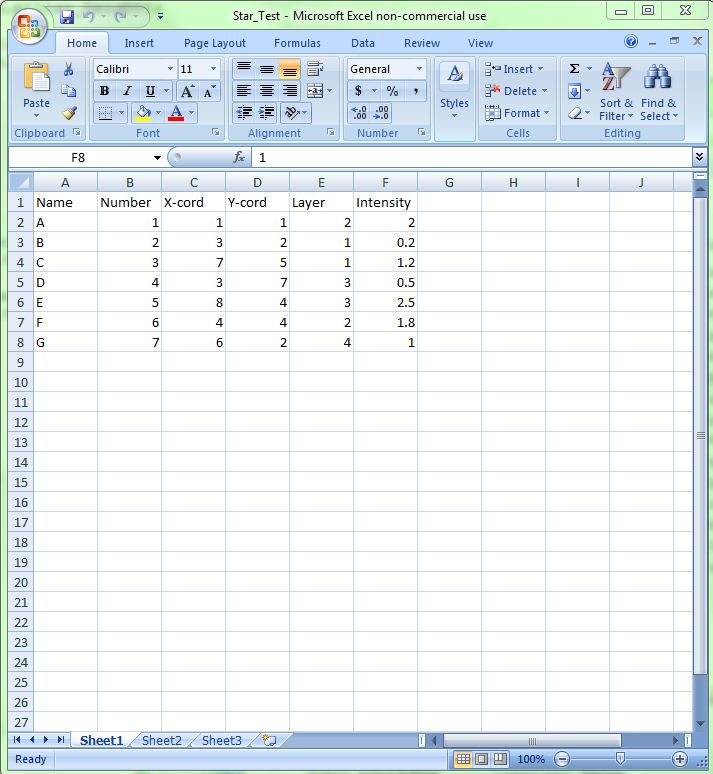
Star Test Data Excel.JPG
